ekremkara22/RFID_Personel/esp32-device/rfid_personel_device/ESP32_RFID_BAGLANTI_SEMASI_A4.png

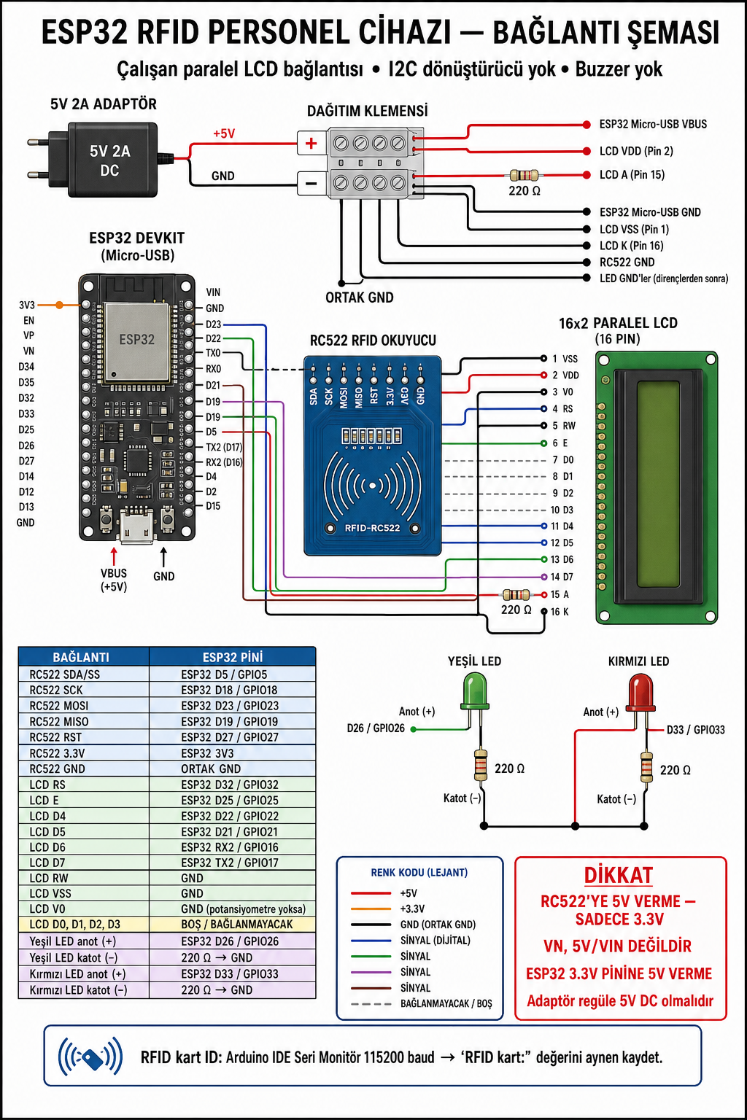
esp32-device/rfid_personel_device/ESP32_RFID_BAGLANTI_SEMASI_A4.png
