ekremkara22/RFID_Personel/esp32-device/rfid_personel_device/ESP32_RFID_BAGLANTI_SEMASI_A4_BUZZER.png

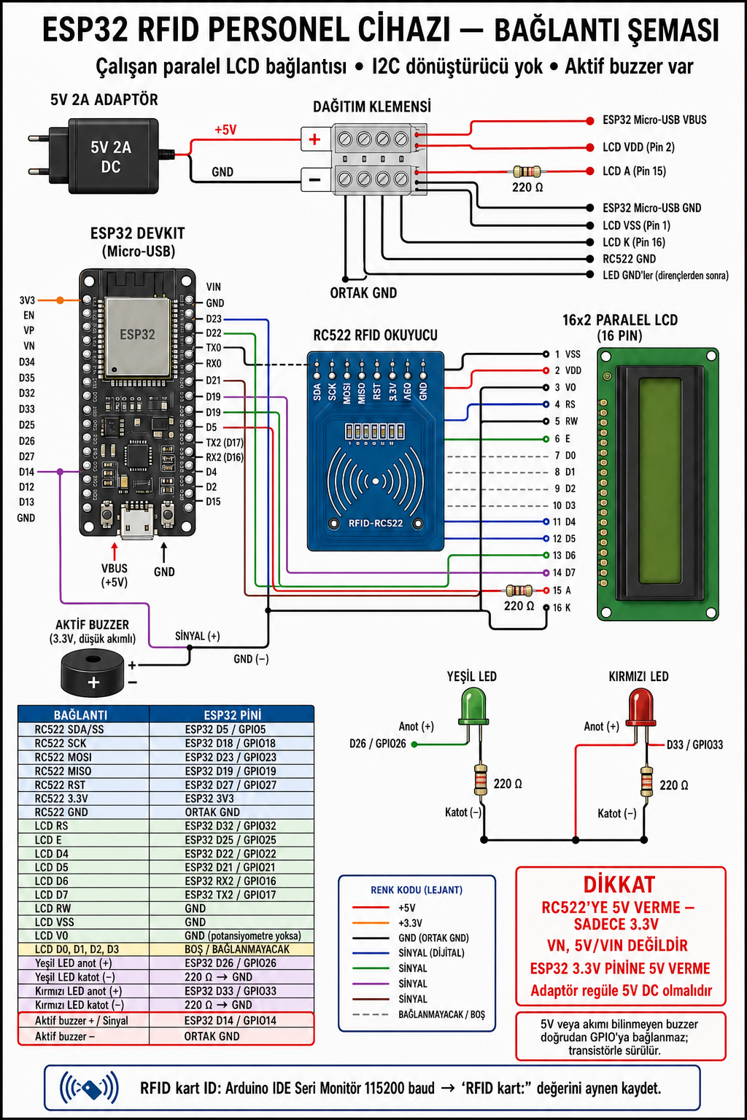
esp32-device/rfid_personel_device/ESP32_RFID_BAGLANTI_SEMASI_A4_BUZZER.png
