ekremkara22/RFID_Personel/tanitim/01-operasyon-ozeti.jpg

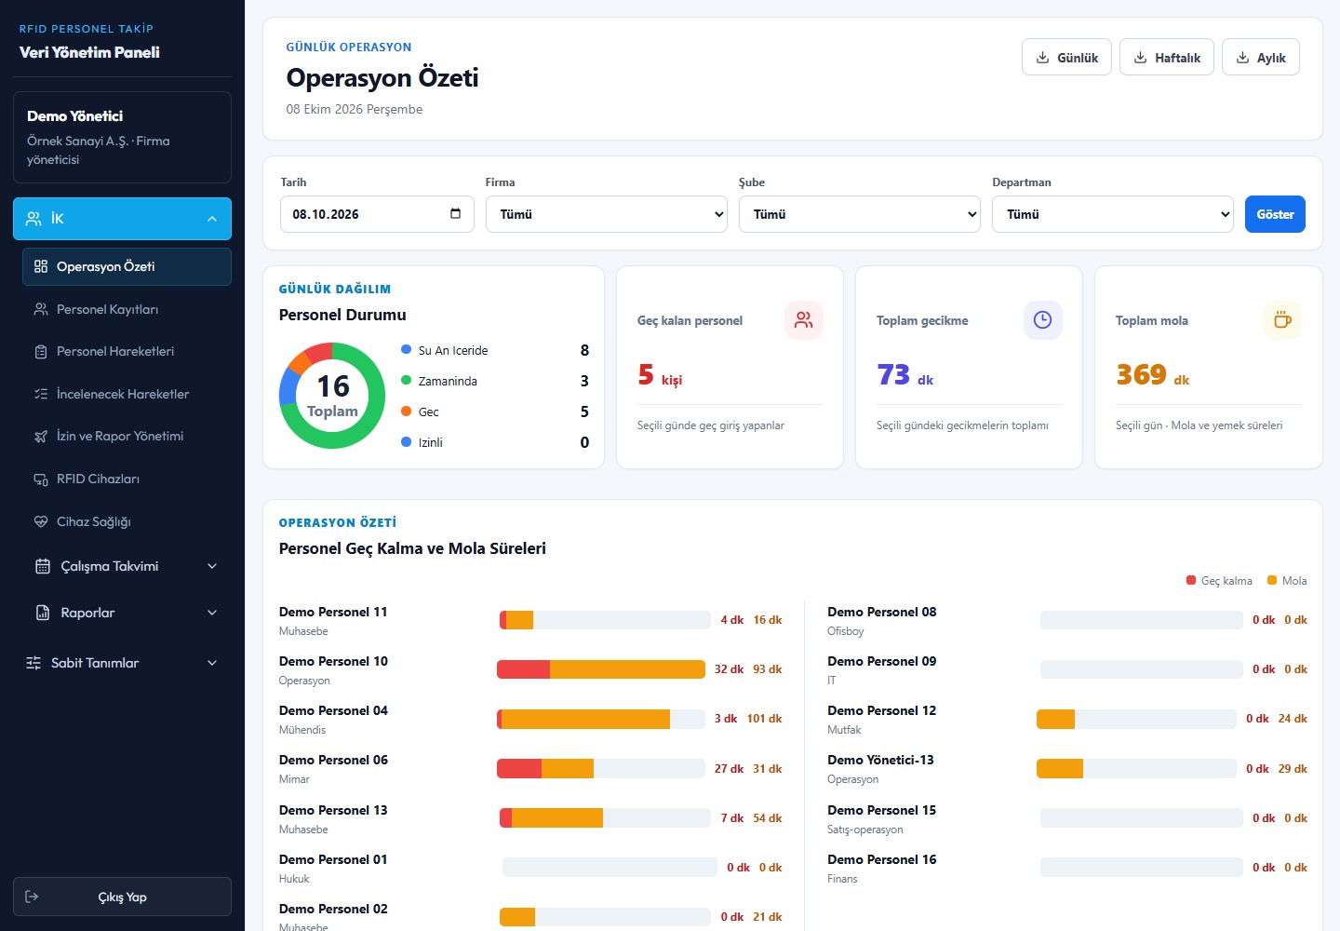
tanitim/01-operasyon-ozeti.jpg
