ekremkara22/RFID_Personel/tanitim/02-personel-kayitlari.jpg

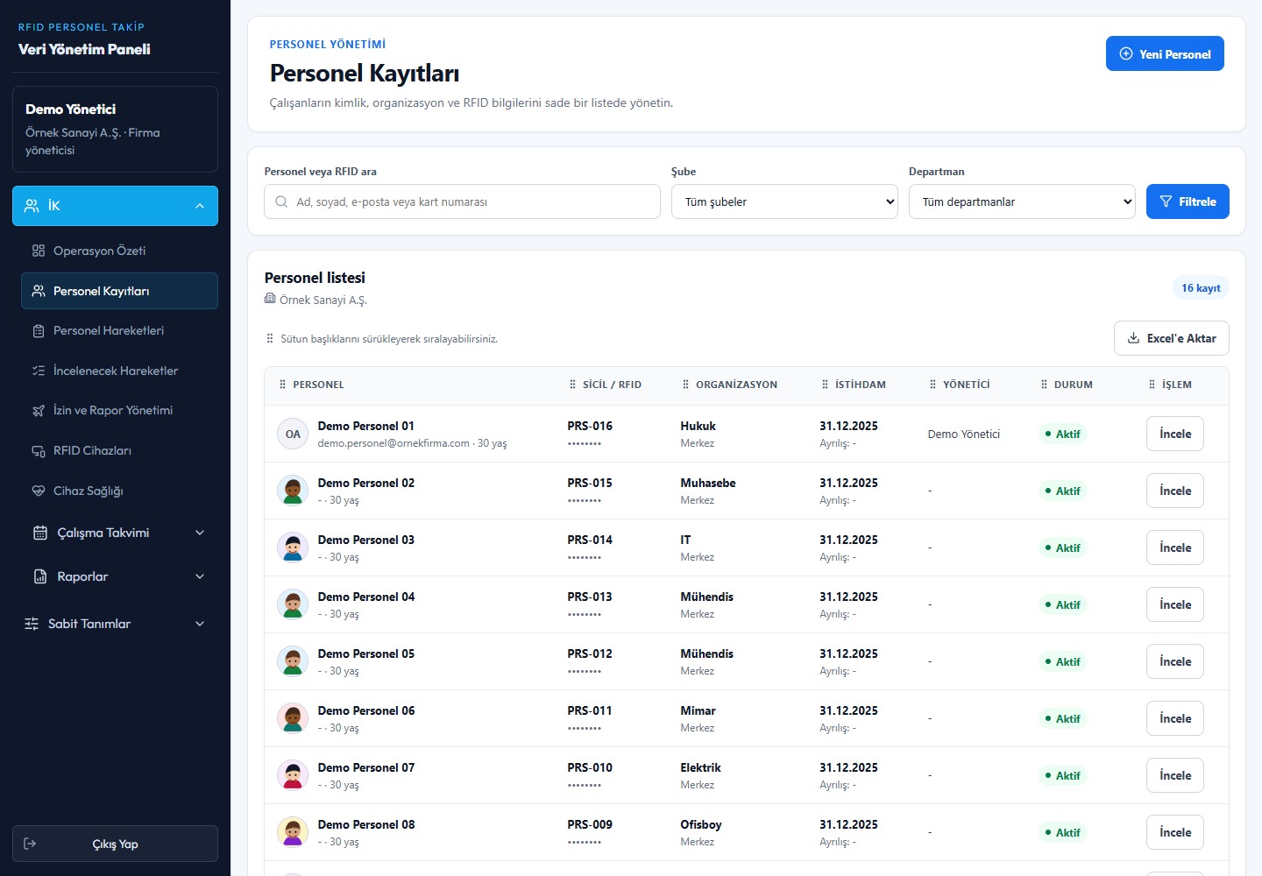
tanitim/02-personel-kayitlari.jpg
