ekremkara22/RFID_Personel/tanitim/03-personel-hareketleri.jpg

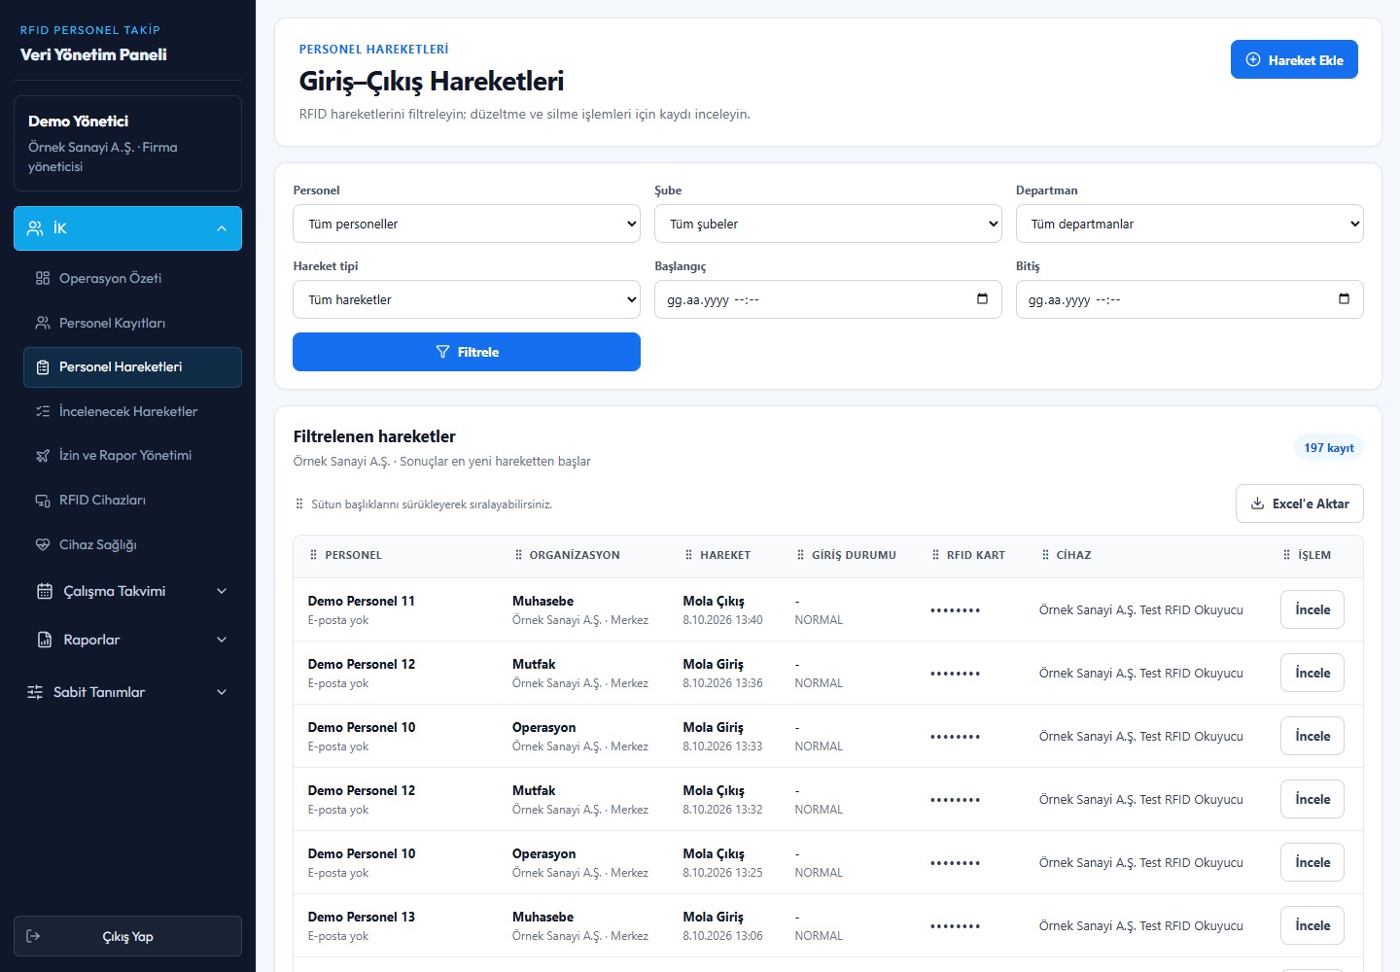
tanitim/03-personel-hareketleri.jpg
