ekremkara22/RFID_Personel/tanitim/04-calisma-takvimi.jpg

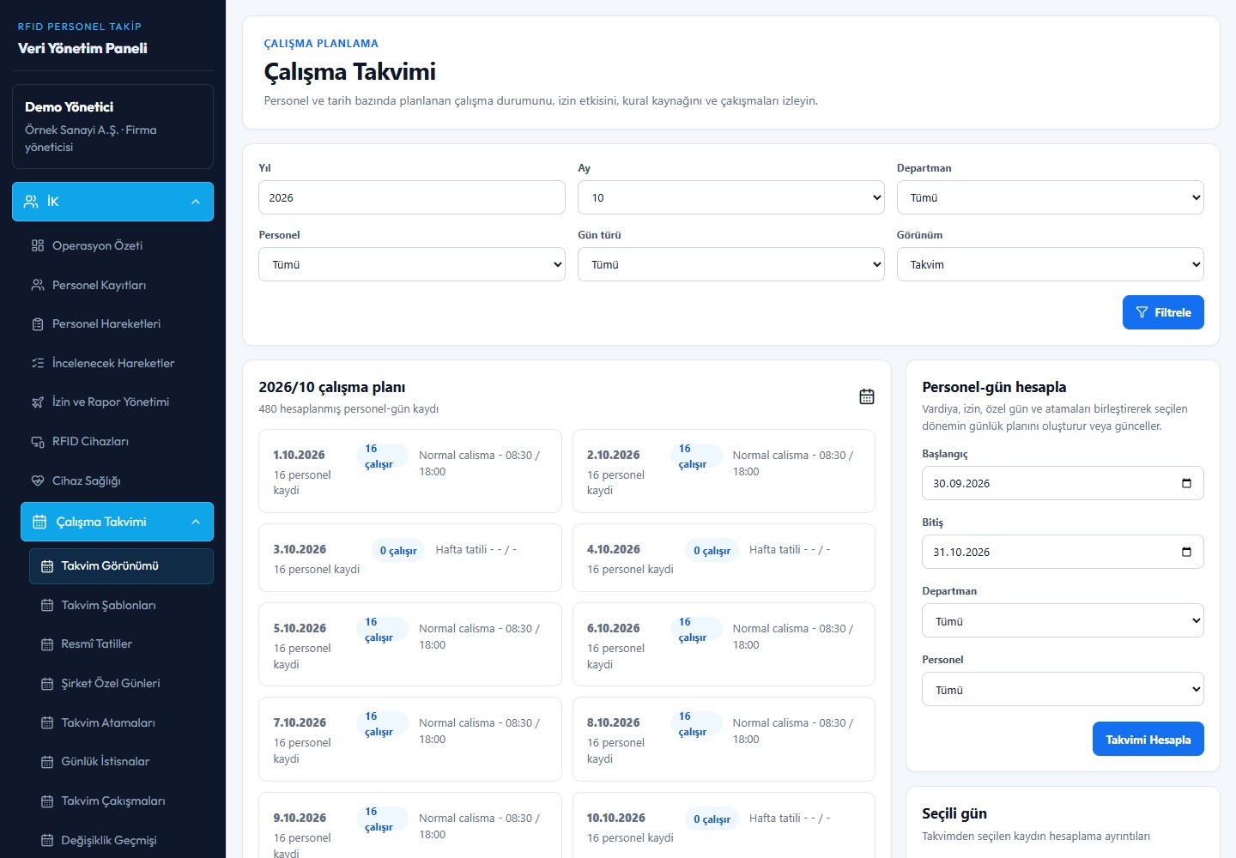
tanitim/04-calisma-takvimi.jpg
