ekremkara22/RFID_Personel/tanitim/05-rfid-cihazlari.jpg

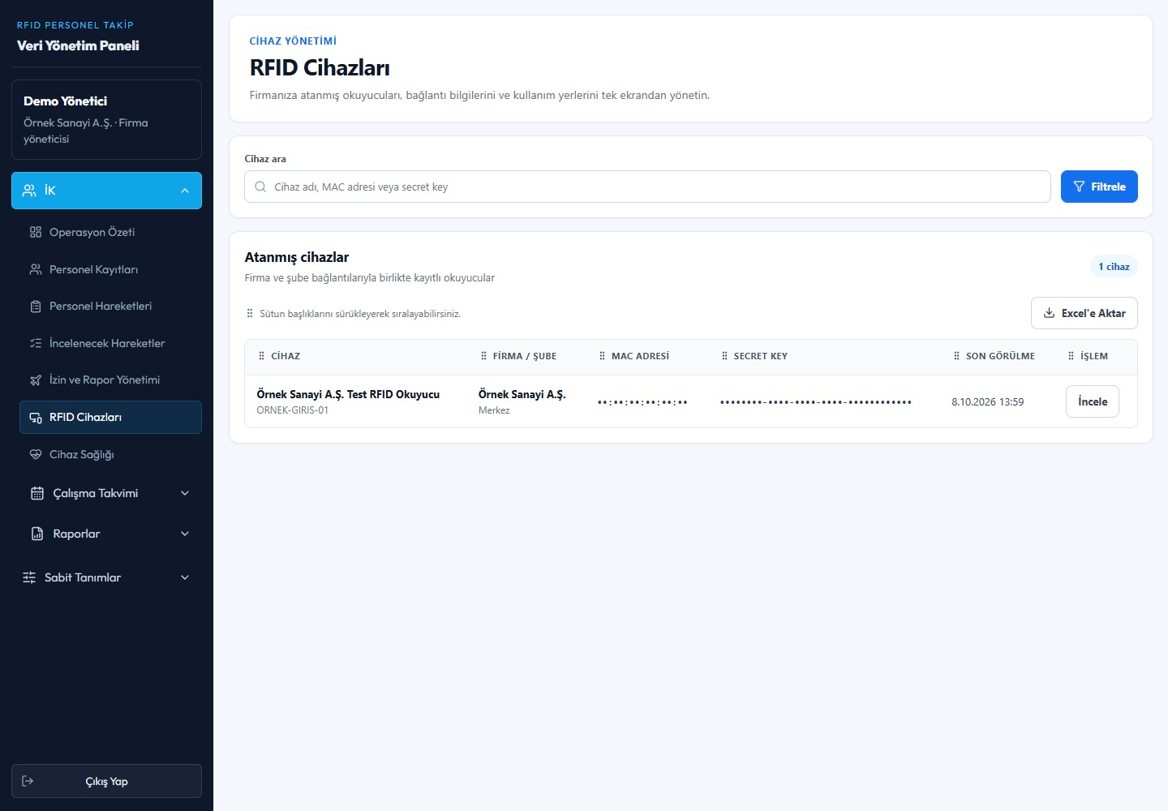
tanitim/05-rfid-cihazlari.jpg
