ekremkara22/RFID_Personel/tanitim/06-gunluk-puantaj-raporu.jpg

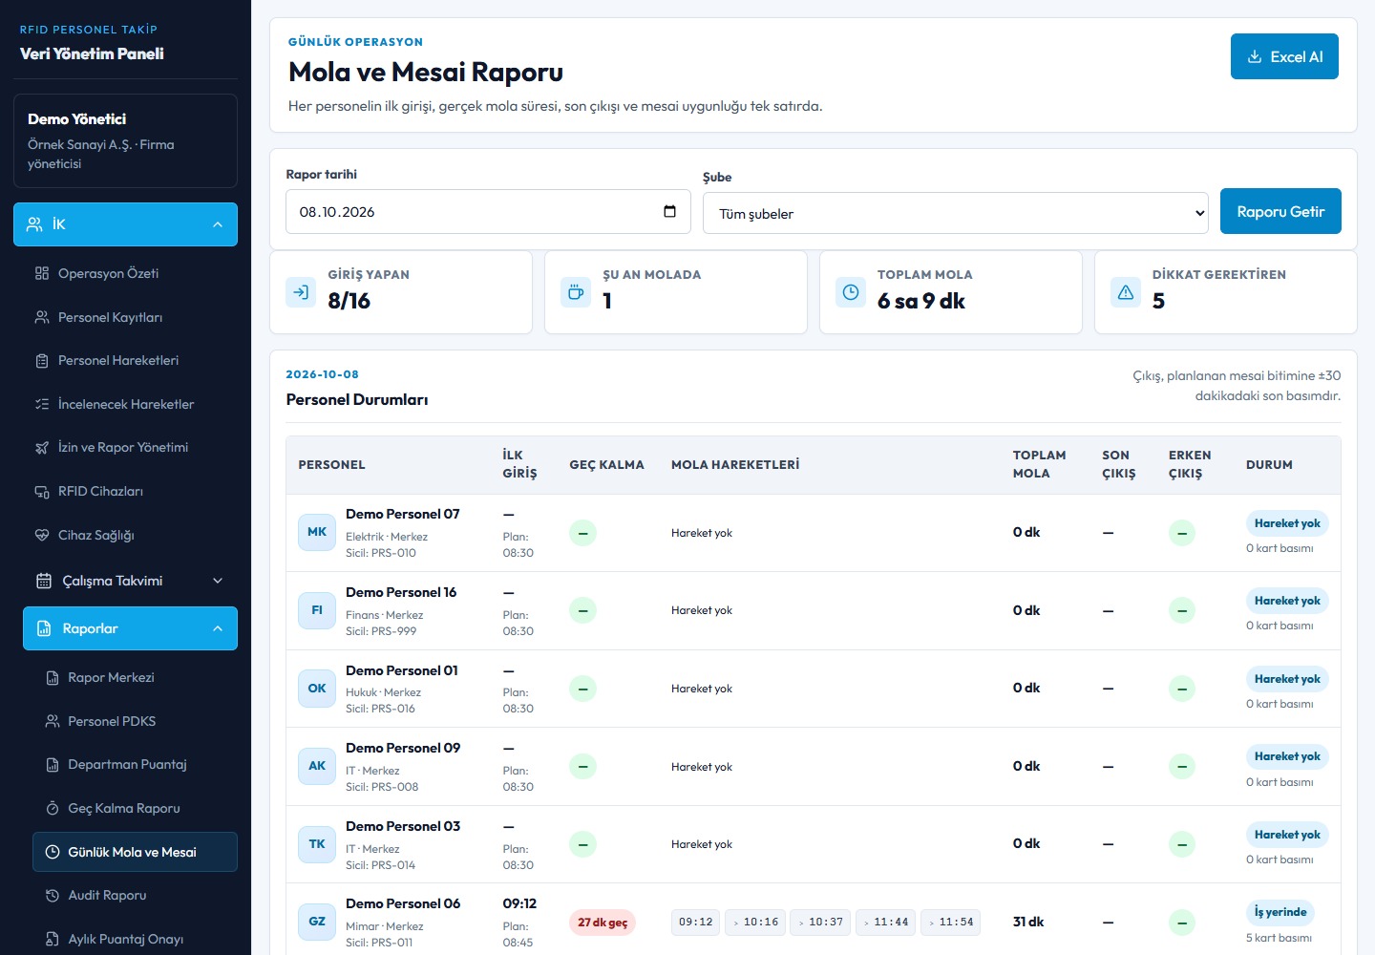
tanitim/06-gunluk-puantaj-raporu.jpg
