ekremkara22/RFID_Personel/UrunGorsel/Gorseller/WhatsApp Image 2026-09-24 at 16.05.17.jpeg

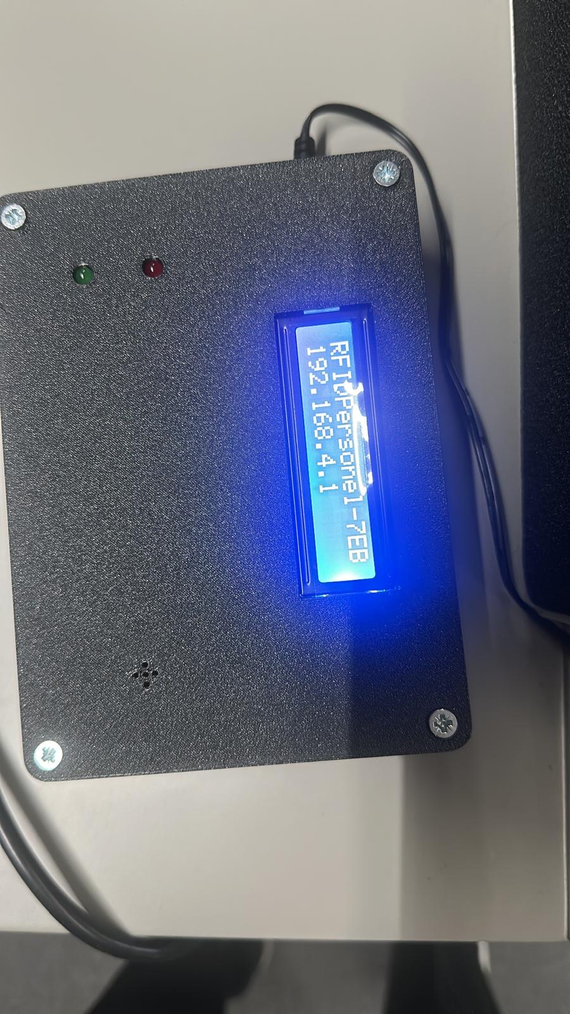
UrunGorsel/Gorseller/WhatsApp Image 2026-09-24 at 16.05.17.jpeg
