ekremkara22/RFID_Personel/UrunGorsel/Gorseller/WhatsApp Image 2026-09-24 at 16.05.19 (2).jpeg

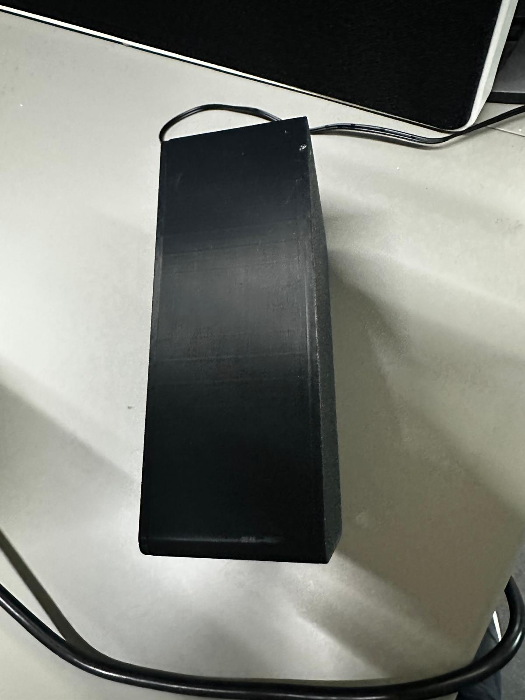
UrunGorsel/Gorseller/WhatsApp Image 2026-09-24 at 16.05.19 (2).jpeg
