ekremkara22/RFID_Personel/UrunGorsel/Tanitim/flodeska-giris-ekrani.png

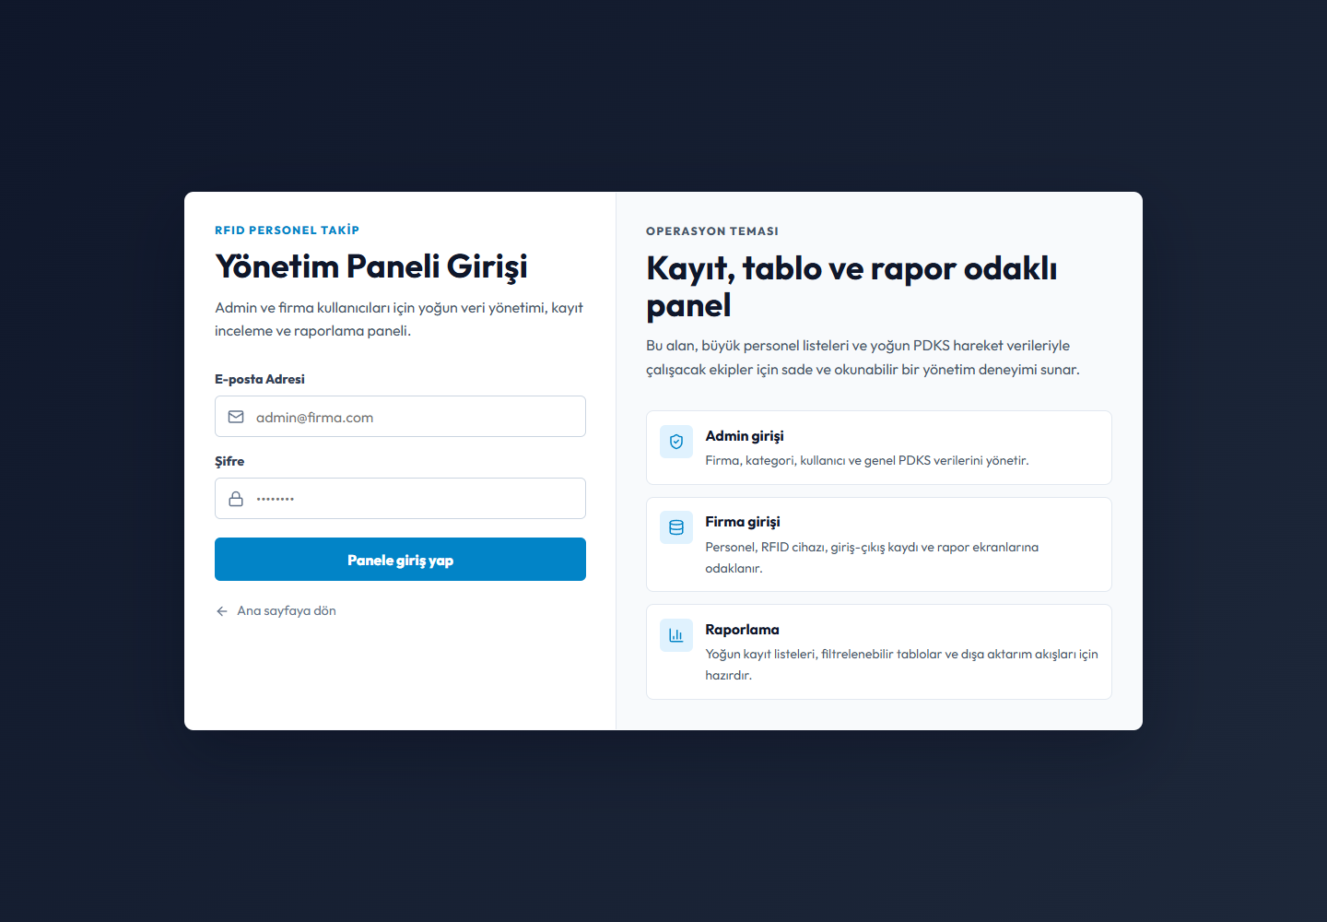
UrunGorsel/Tanitim/flodeska-giris-ekrani.png
