ekremkara22/RFID_Personel/UrunGorsel/Tanitim/flodeska-operasyon-tam-demo.png

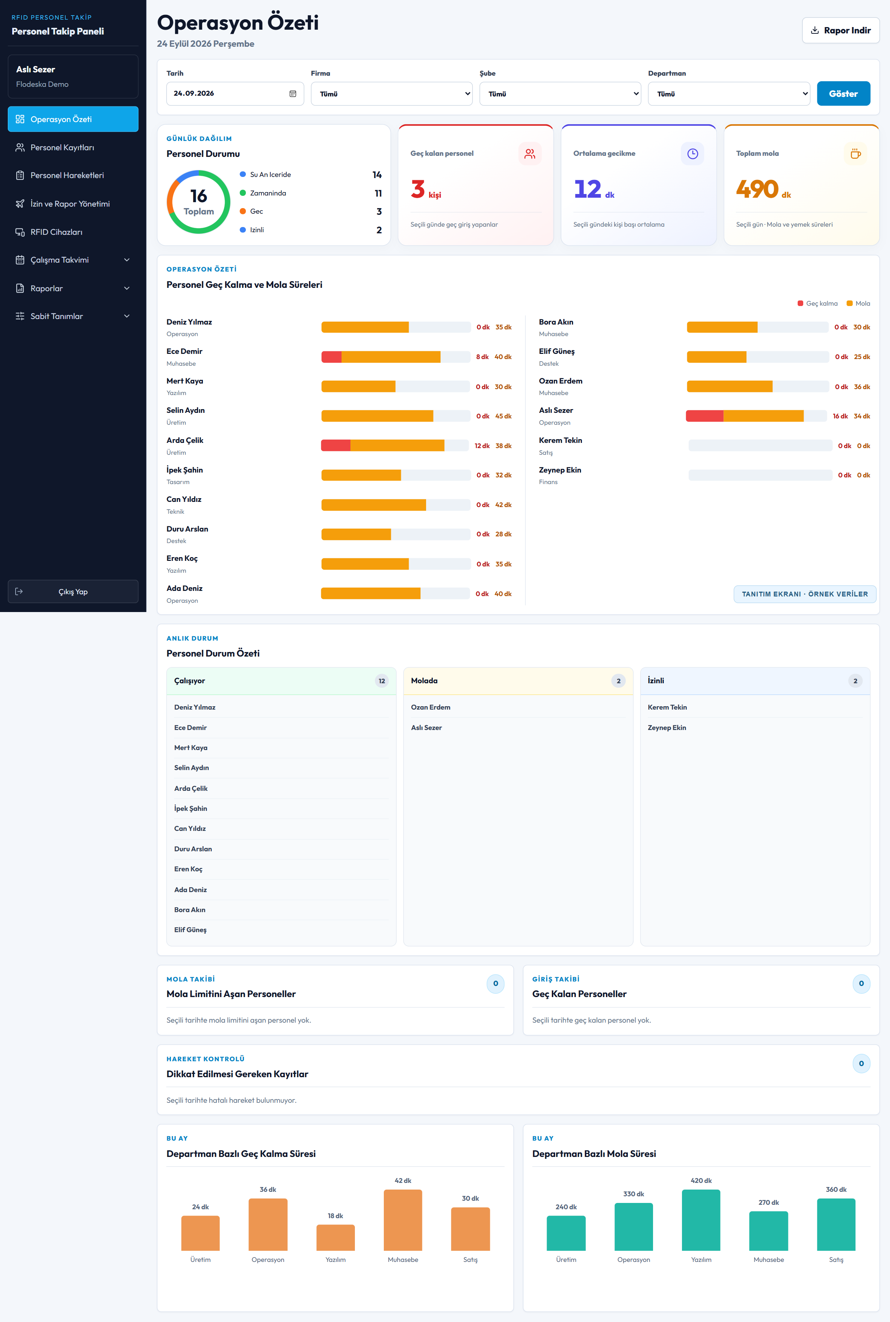
UrunGorsel/Tanitim/flodeska-operasyon-tam-demo.png
