ekremkara22/RFID_Personel/UrunGorsel/Tanitim/Gemini_Generated_Image_42sssy42sssy42ss.jpg

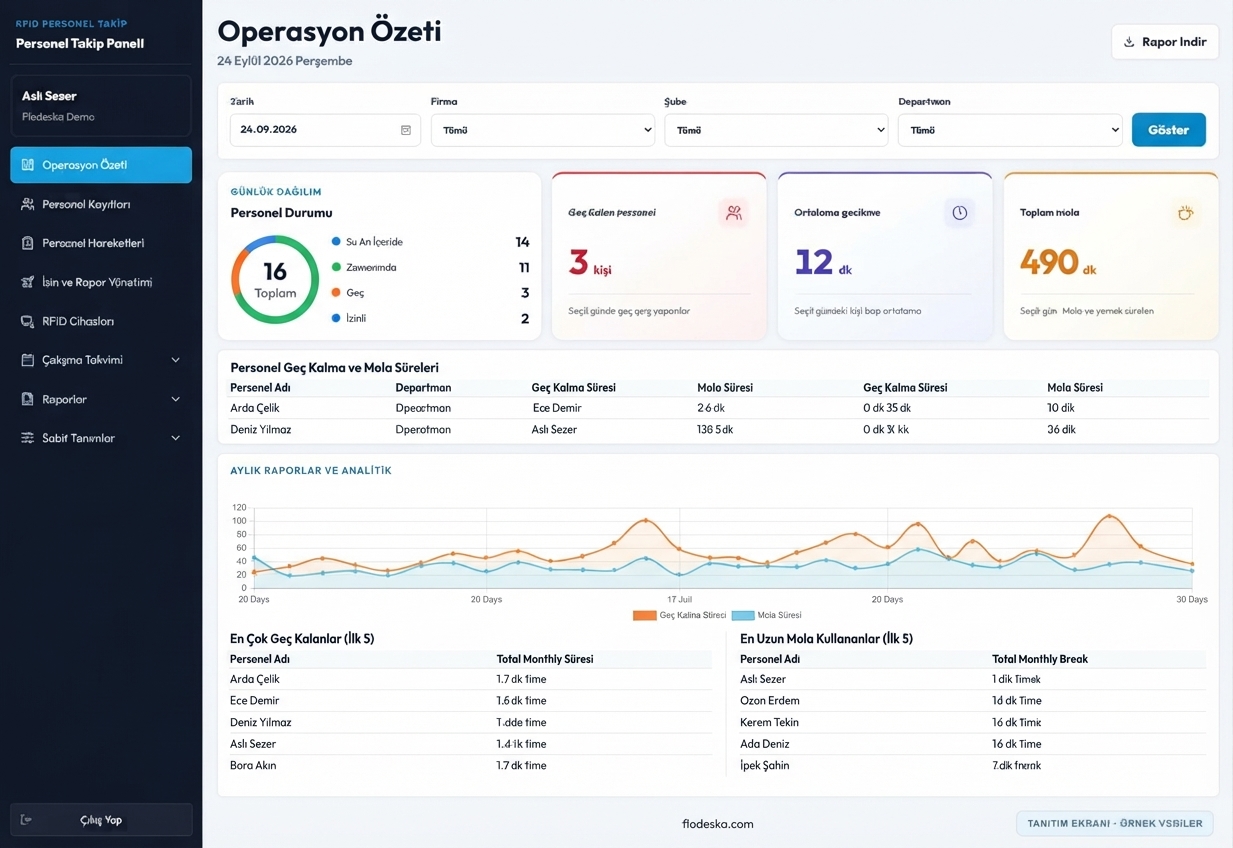
UrunGorsel/Tanitim/Gemini_Generated_Image_42sssy42sssy42ss.jpg
