ekremkara22/RFID_Personel/UrunGorsel/Tanitim/Gemini_Generated_Image_69umsy69umsy69um.jpg

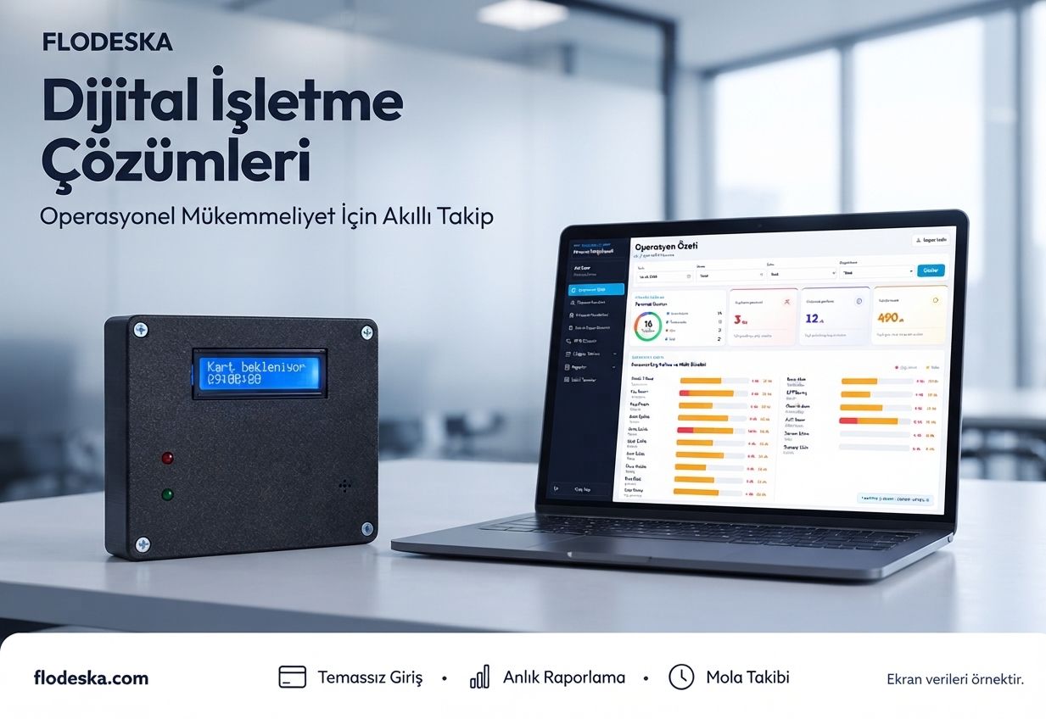
UrunGorsel/Tanitim/Gemini_Generated_Image_69umsy69umsy69um.jpg
