ekremkara22/RFID_Personel/UrunGorsel/Tanitim/Gemini_Generated_Image_a233iia233iia233.jpg

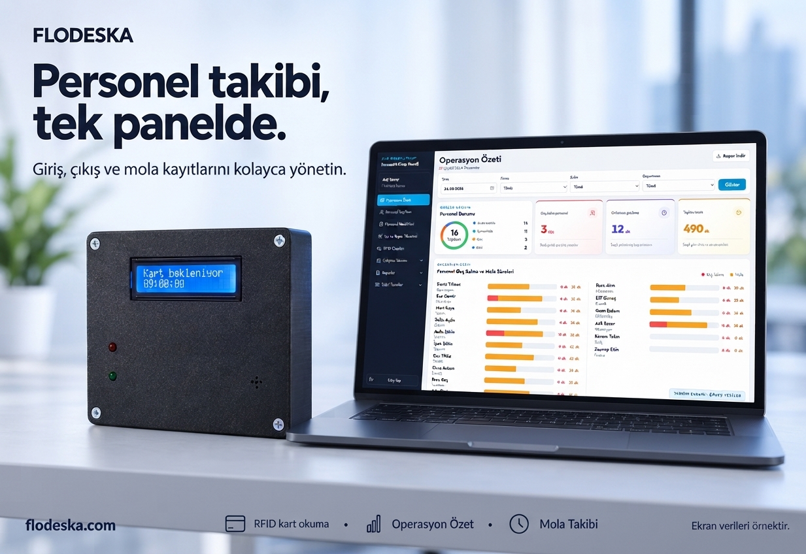
UrunGorsel/Tanitim/Gemini_Generated_Image_a233iia233iia233.jpg
