ekremkara22/RFID_Personel/esp32-device/rfid_personel_device_ota_v1_2_0/ota_root_ca.h

#pragma once

// Let's Encrypt ISRG Root X1, valid until 2035-06-04.
static const char OTA_ROOT_CA[] PROGMEM = R"CERT(
-----BEGIN CERTIFICATE-----
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
-----END CERTIFICATE-----
)CERT";
